roman-oberenkowski/multiplexing-demo-seven-segment/Schematic/KicadProject/7segDemoSchematic.kicad_sch

## KiCad design Schematic/KicadProject/7segDemoSchematic.kicad_sch (2023-11-08)

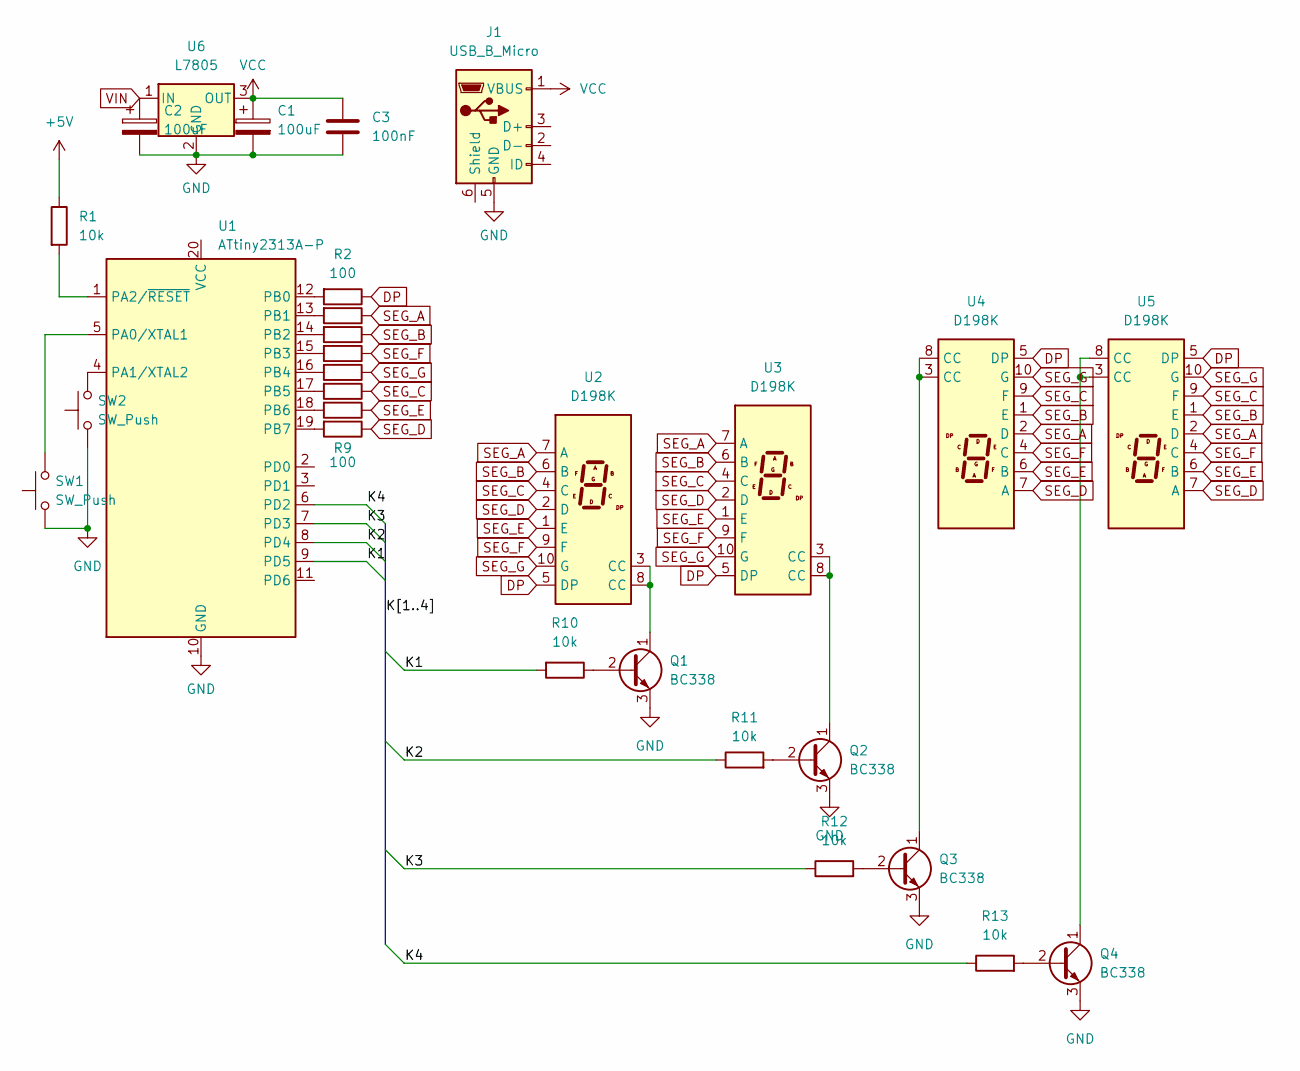
[picture p5: schematic 7segDemoSchematic.kicad_sch]

Parts:
C1, C2: 100uF
C3: 100nF
J1: USB_B_Micro
Q1, Q2, Q3, Q4: BC338; TO-92_Inline
R1, R10, R11, R12, R13: 10k
R2, R9: 100
R3, R4, R5, R6, R7, R8: R
SW1, SW2: SW_Push
U1: ATtiny2313A-P; DIP-20_W7.62mm
U2, U3, U4, U5: D198K; D1X8K
U6: L7805

Connections:
+5V: R1.1
DP: R2.1, U2.5 (DP), U3.5 (DP), U4.5 (DP), U5.5 (DP)
GND: C1.2, C2.2, C3.2, J1.5 (GND), Q1.3 (E), Q2.3 (E), Q3.3 (E), Q4.3 (E), SW1.1, SW2.1, U1.10 (GND), U6.2 (GND)
K1: R10.2, U1.9 (PD5)
K2: R11.1, U1.8 (PD4)
K3: R12.1, U1.7 (PD3)
K4: R13.1, U1.6 (PD2)
unnamed: Q1.1 (C), U2.3 (CC), U2.8 (CC)
unnamed: Q1.2 (B), R10.1
unnamed: Q2.1 (C), U3.3 (CC), U3.8 (CC)
unnamed: Q2.2 (B), R11.2
unnamed: Q3.1 (C), U4.3 (CC), U4.8 (CC)
unnamed: Q3.2 (B), R12.2
unnamed: Q4.1 (C), U5.3 (CC), U5.8 (CC)
unnamed: Q4.2 (B), R13.2
unnamed: R1.2, U1.1 (PA2/~RESET)
unnamed: R2.2, U1.12 (PB0)
unnamed: R3.2, U1.13 (PB1)
unnamed: R4.2, U1.14 (PB2)
unnamed: R5.2, U1.15 (PB3)
unnamed: R6.2, U1.16 (PB4)
unnamed: R7.2, U1.17 (PB5)
unnamed: R8.2, U1.18 (PB6)
unnamed: R9.2, U1.19 (PB7)
unnamed: SW1.2, U1.5 (PA0/XTAL1)
unnamed: SW2.2, U1.4 (PA1/XTAL2)
SEG_A: R3.1, U2.7 (A), U3.7 (A), U4.2 (D), U5.2 (D)
SEG_B: R4.1, U2.6 (B), U3.6 (B), U4.1 (E), U5.1 (E)
SEG_C: R7.1, U2.4 (C), U3.4 (C), U4.9 (F), U5.9 (F)
SEG_D: R9.1, U2.2 (D), U3.2 (D), U4.7 (A), U5.7 (A)
SEG_E: R8.1, U2.1 (E), U3.1 (E), U4.6 (B), U5.6 (B)
SEG_F: R5.1, U2.9 (F), U3.9 (F), U4.4 (C), U5.4 (C)
SEG_G: R6.1, U2.10 (G), U3.10 (G), U4.10 (G), U5.10 (G)
VCC: C1.1, C3.1, J1.1 (VBUS), U6.3 (OUT)
VIN: C2.1, U6.1 (IN)
